flo-bit/buttfinity/stls/lids/switches/buttfinity-1x1-1-round-self-locking-switch-lid.stl

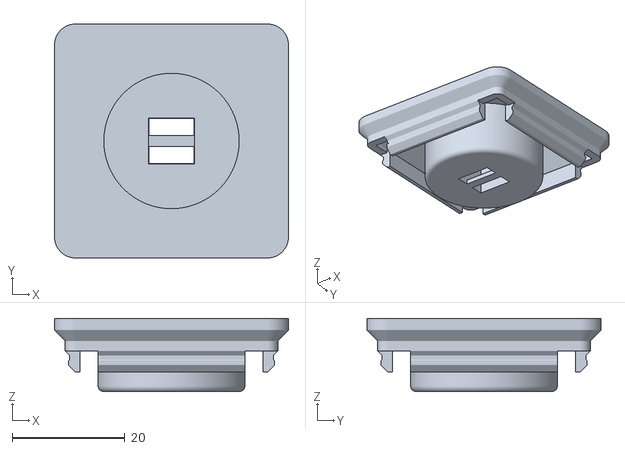
[picture p15: CAD file, 2025-09-28]
stls/lids/switches/buttfinity-1x1-1-round-self-locking-switch-lid.stl
41.5 x 41.5 x 13.0
