flo-bit/buttfinity/stls/lids/caps/buttfinity-mx-switch-round-cap-23mm.stl

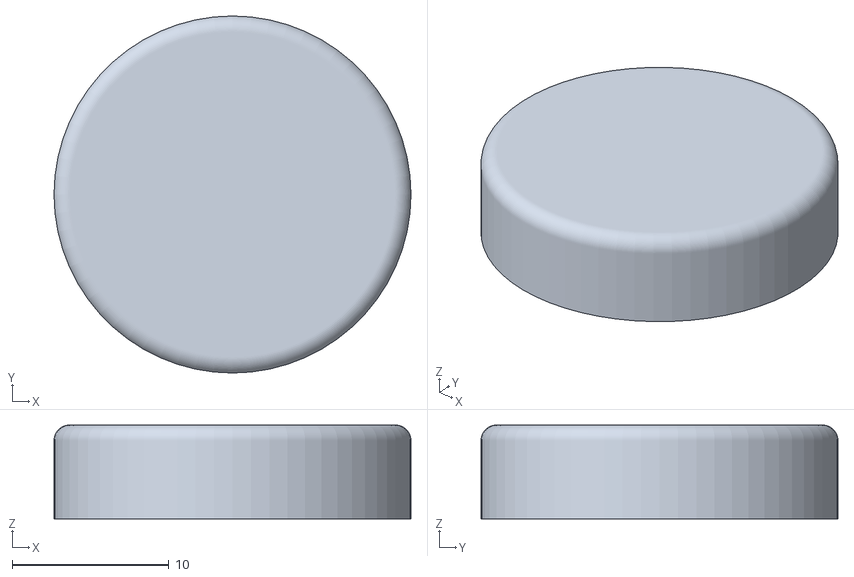
[picture p16: CAD file, 2025-09-28]
stls/lids/caps/buttfinity-mx-switch-round-cap-23mm.stl
22.8 x 22.8 x 6.00
