flo-bit/buttfinity/stls/lids/caps/buttfinity-mx-switch-square-cap-15x33mm.stl

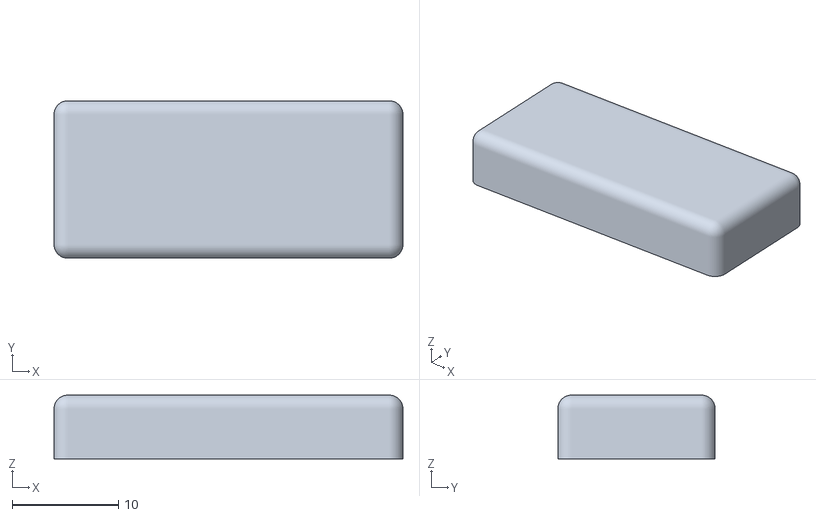
[picture p17: CAD file, 2025-09-28]
stls/lids/caps/buttfinity-mx-switch-square-cap-15x33mm.stl
32.8 x 14.8 x 6.00
